linux-automation/candleLightFD/release/candlelightfd-S01-R01/candlelightfd-P01-R01-V01/pdf/candlelightfd-P01-R01-V01_Edge.Cuts.pdf

git: hardware/candlelightfd-S01_candlelightfd State:release
Date:2022-03-07
